WeymenKoo/Rover-Project/Solidworks CAD Rev 1/92mm-case-fan-1.snapshot.2/F9 render.JPG

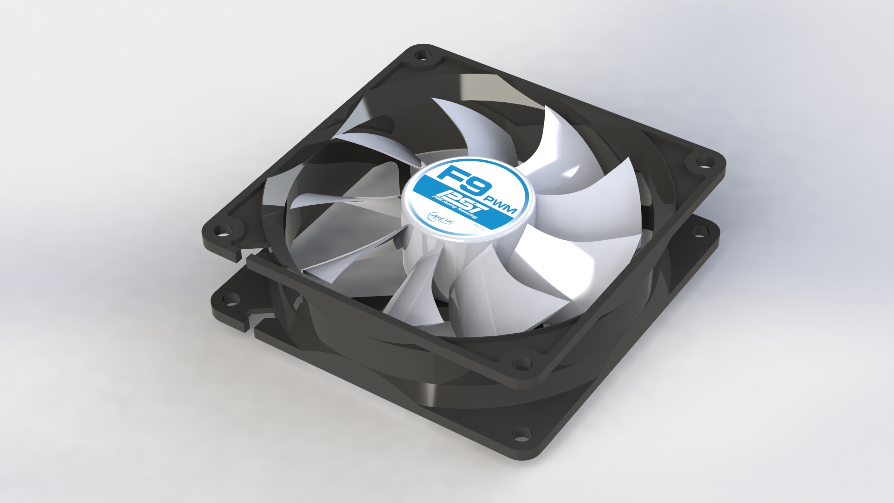
Solidworks CAD Rev 1/92mm-case-fan-1.snapshot.2/F9 render.JPG
