WeymenKoo/Rover-Project/Solidworks CAD Rev 1/arduino-mega-2560--1.snapshot.8/Renderings/Arduino MEGA2560 CHRISTMAS2.png

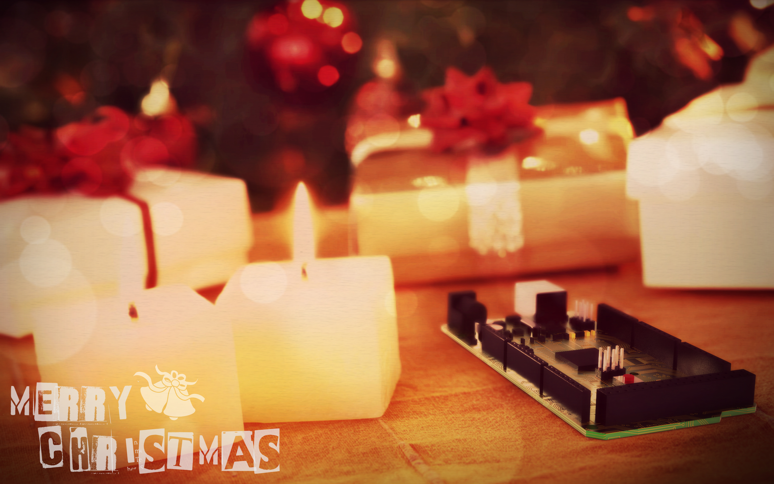
Solidworks CAD Rev 1/arduino-mega-2560--1.snapshot.8/Renderings/Arduino MEGA2560 CHRISTMAS2.png
