WeymenKoo/Rover-Project/Solidworks CAD Rev 1/arduino-mega-2560--1.snapshot.8/Renderings/Mega2.JPG

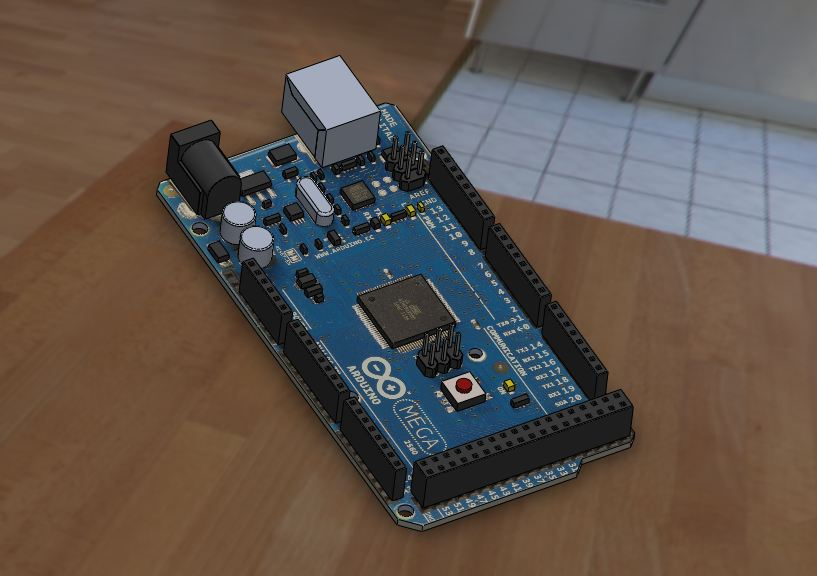
Solidworks CAD Rev 1/arduino-mega-2560--1.snapshot.8/Renderings/Mega2.JPG
