WeymenKoo/Rover-Project/Solidworks CAD Rev 1/breadboard-15.snapshot.1/Breadboard 3D View.JPG

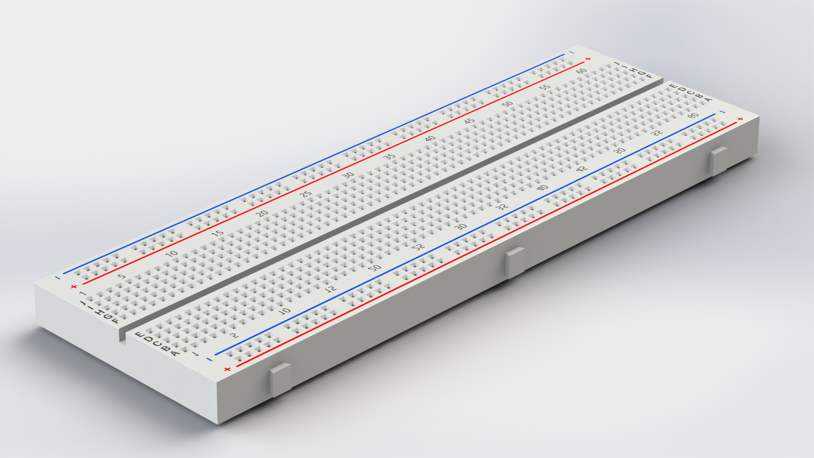
Solidworks CAD Rev 1/breadboard-15.snapshot.1/Breadboard 3D View.JPG
