WeymenKoo/Rover-Project/STL/ChasisFront.STL

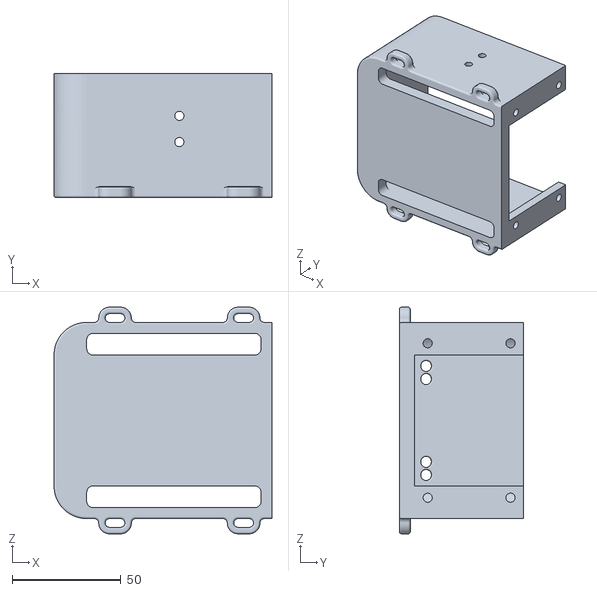
[picture p25: CAD file, 2022-04-02]
STL/ChasisFront.STL
100.0 x 57.0 x 104.0
