WeymenKoo/Rover-Project/Motor sizing/37d-gearmotor-3d-models/37d-gearmotor-100-131-150.step

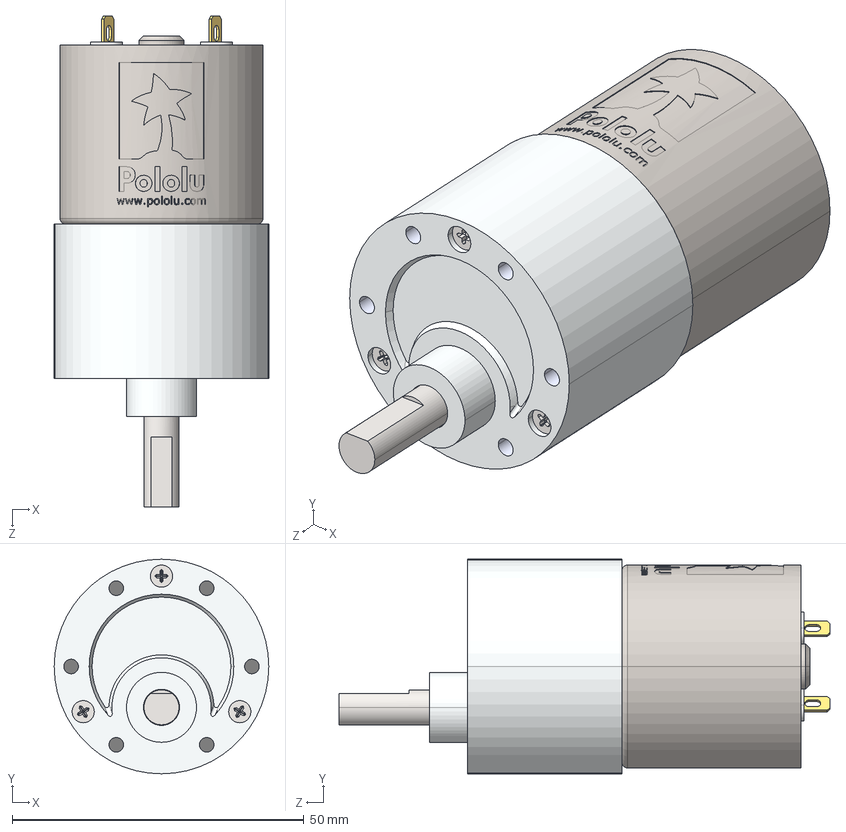
[picture p26: CAD file, 2022-04-02]
Motor sizing/37d-gearmotor-3d-models/37d-gearmotor-100-131-150.step
36.8 x 36.8 x 84.2 mm
