WeymenKoo/Rover-Project/Solidworks CAD Rev 1/AckermanSteering-Servo Mount.SLDPRT

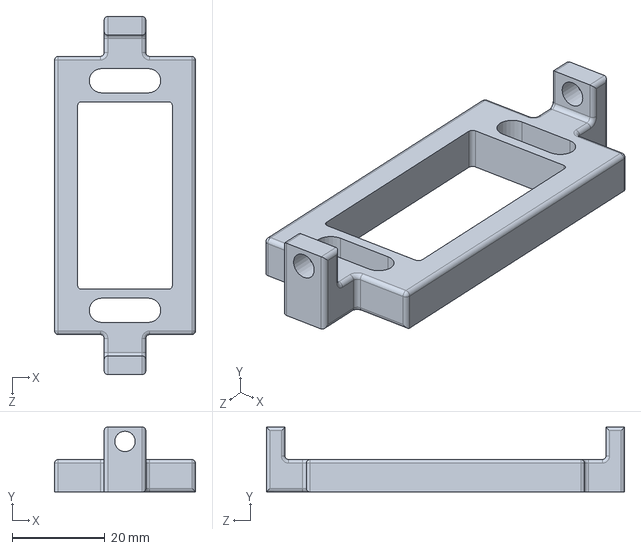
[picture p27: CAD file, 2023-01-30]
Solidworks CAD Rev 1/AckermanSteering-Servo Mount.SLDPRT
30.4 x 14.0 x 77.2 mm
