WeymenKoo/Rover-Project/STL/Frontwheelshaft.STL

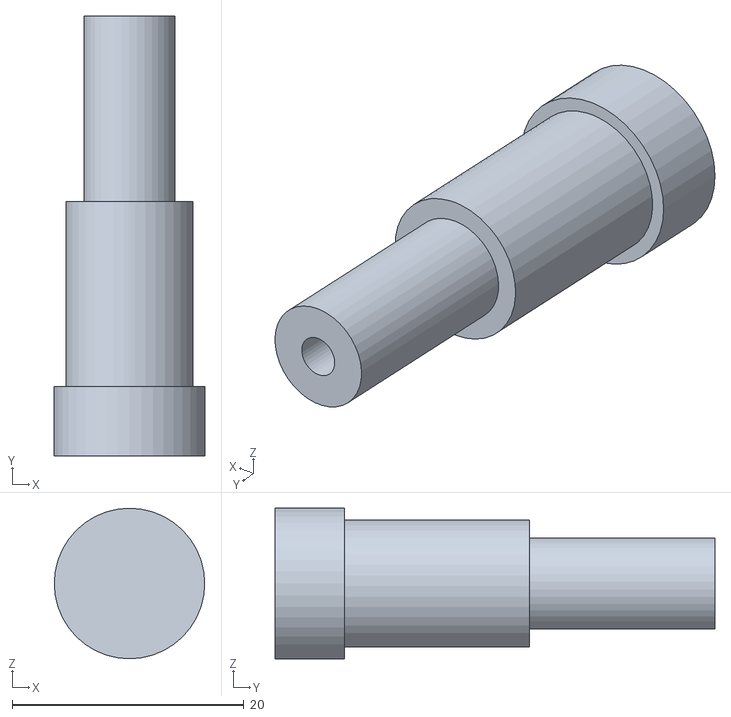
[picture p28: CAD file, 2022-04-02]
STL/Frontwheelshaft.STL
13.0 x 38.0 x 13.0
