WeymenKoo/Rover-Project/Motor sizing/37d-gearmotor-3d-models/37d-gearmotor-6-10.step

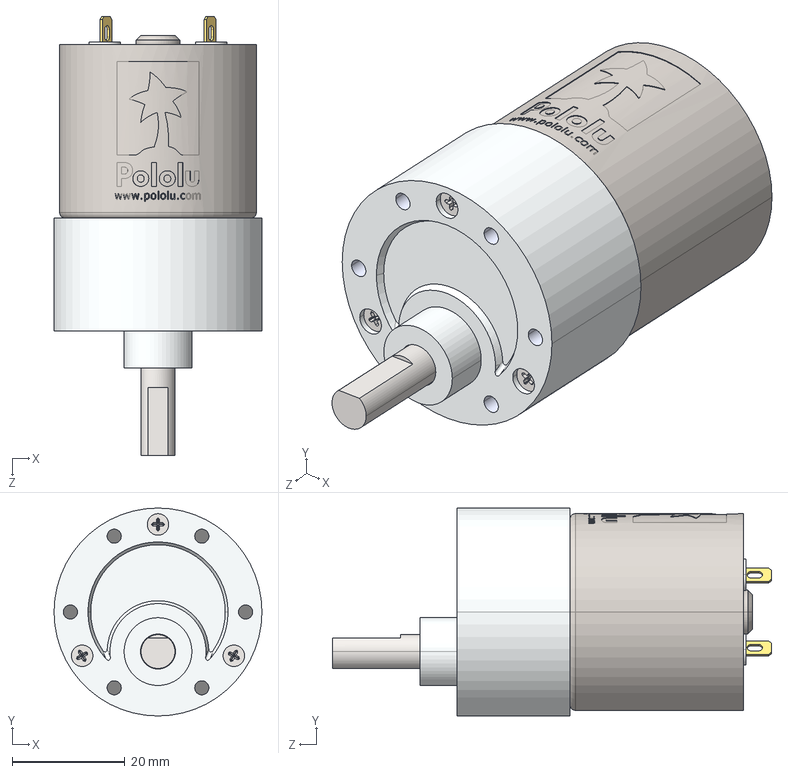
[picture p29: CAD file, 2022-04-02]
Motor sizing/37d-gearmotor-3d-models/37d-gearmotor-6-10.step
36.8 x 36.8 x 77.7 mm
