WeymenKoo/Rover-Project/STL/ChasisMid.STL

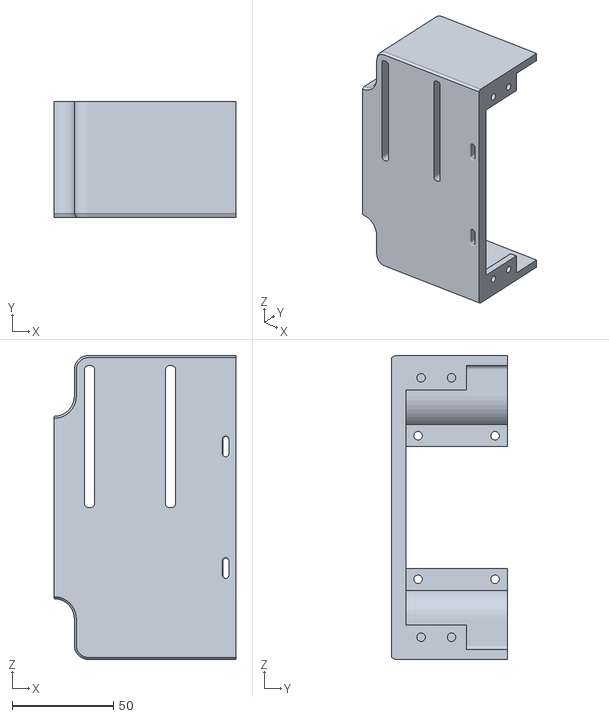
[picture p30: CAD file, 2022-04-02]
STL/ChasisMid.STL
89.7 x 57.0 x 150.0
