WeymenKoo/Rover-Project/Solidworks CAD Rev 1/AckermanSteering-WheelShaft 2.SLDPRT

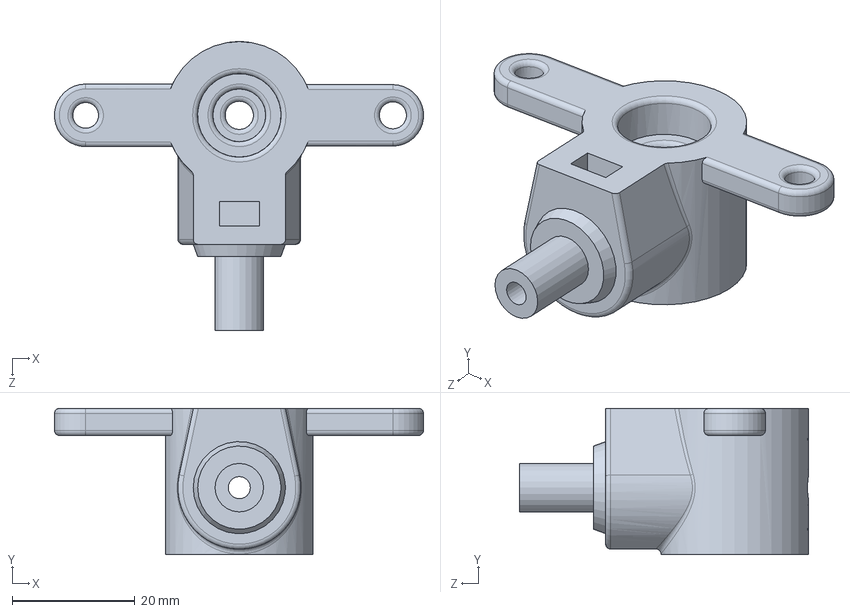
[picture p31: CAD file, 2023-01-30]
Solidworks CAD Rev 1/AckermanSteering-WheelShaft 2.SLDPRT
60.1 x 23.8 x 47.0 mm
