WeymenKoo/Rover-Project/Motor sizing/37d-gearmotor-3d-models/37d-gearmotor-19-30.step

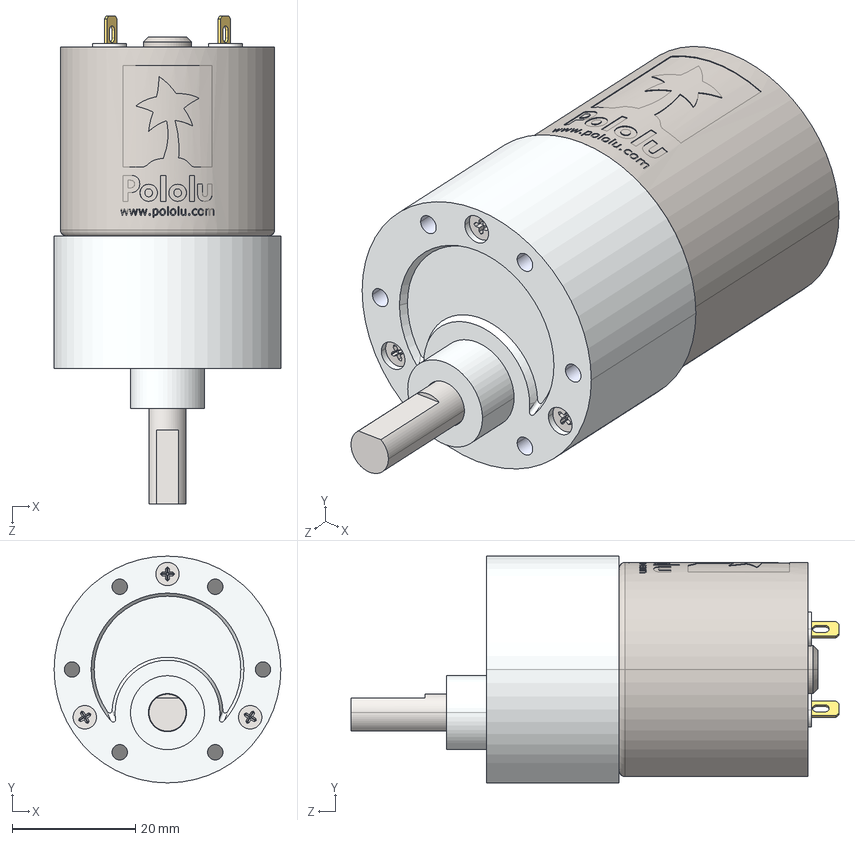
[picture p32: CAD file, 2022-04-02]
Motor sizing/37d-gearmotor-3d-models/37d-gearmotor-19-30.step
36.8 x 36.8 x 79.2 mm
